MarcoLosurdo/DigiSporc/DigiSporc-board.png

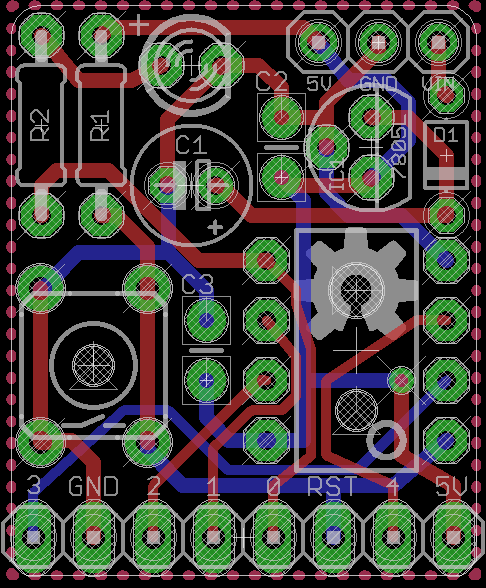
DigiSporc-board.png
