MarcoLosurdo/DigiSporc/DigiSporc.png

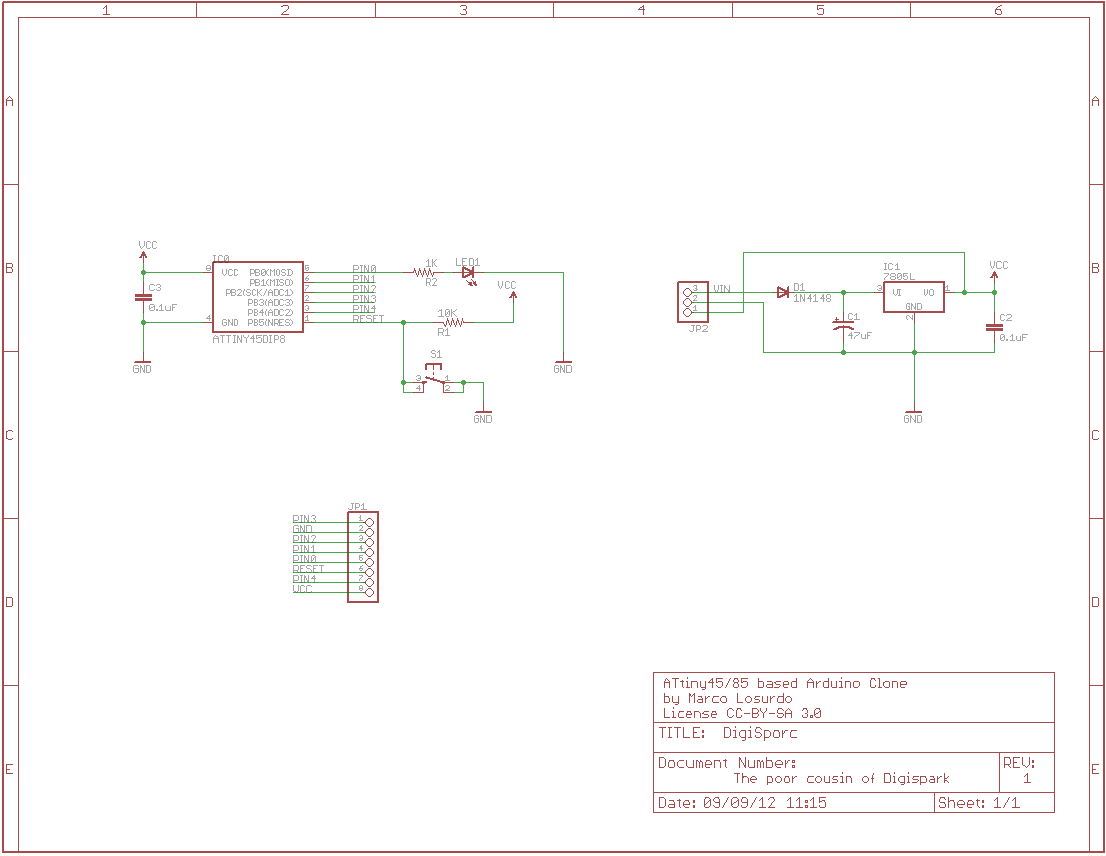
DigiSporc.png
