MarcoLosurdo/DigiSporc/DigiSporc_nano.png

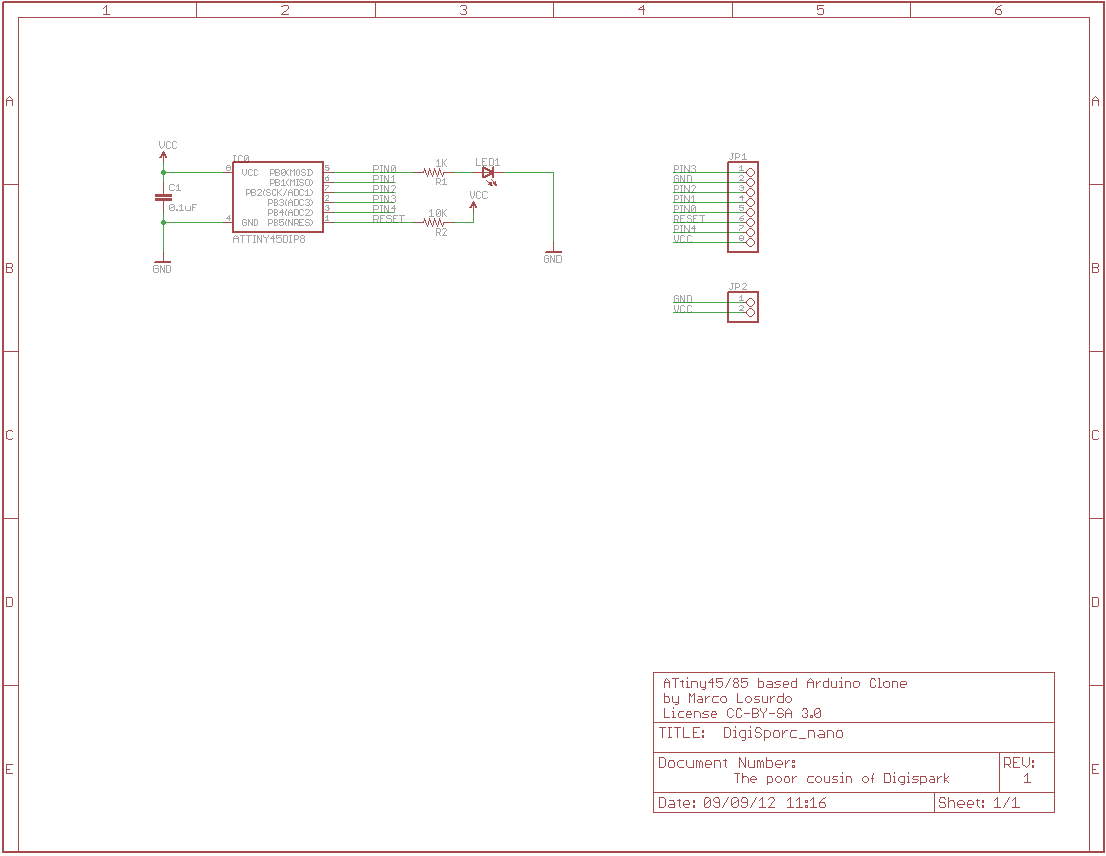
DigiSporc_nano.png
