MarcoLosurdo/DigiSporc/pic/ArduinoAsISP_menu.png

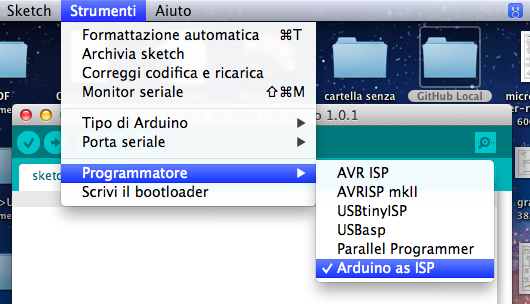
pic/ArduinoAsISP_menu.png
