MarcoLosurdo/DigiSporc/pic/buta.png

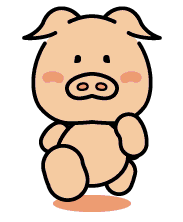
pic/buta.png
