MarcoLosurdo/DigiSporc/pic/DigiSporc proto.jpeg

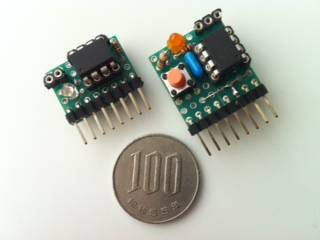
pic/DigiSporc proto.jpeg
