MarcoLosurdo/DigiSporc/pic/DigiSporc.png

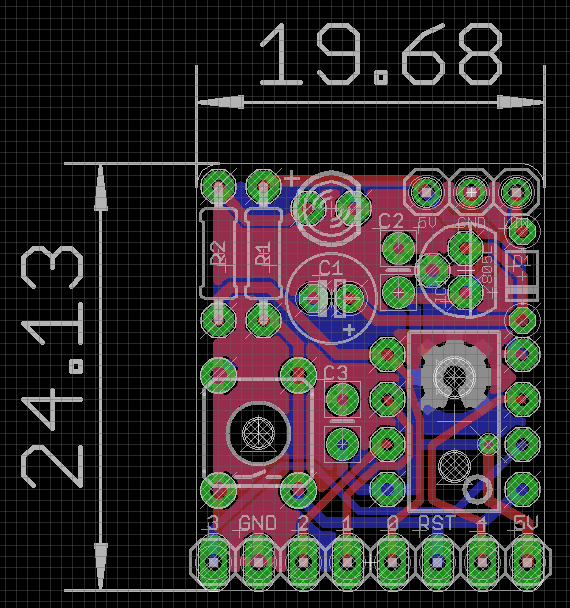
pic/DigiSporc.png
