MarcoLosurdo/DigiSporc/pic/DigiSporc_plugged.jpeg

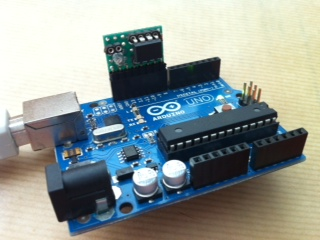
pic/DigiSporc_plugged.jpeg
