MarcoLosurdo/DigiSporc/pic/Lanciami_i_componenti.jpeg

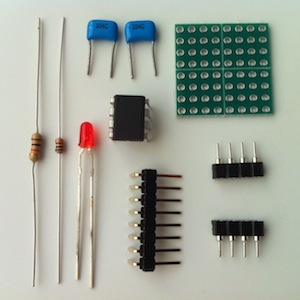
pic/Lanciami_i_componenti.jpeg
