MarcoLosurdo/DigiSporc/pic/proto.jpeg

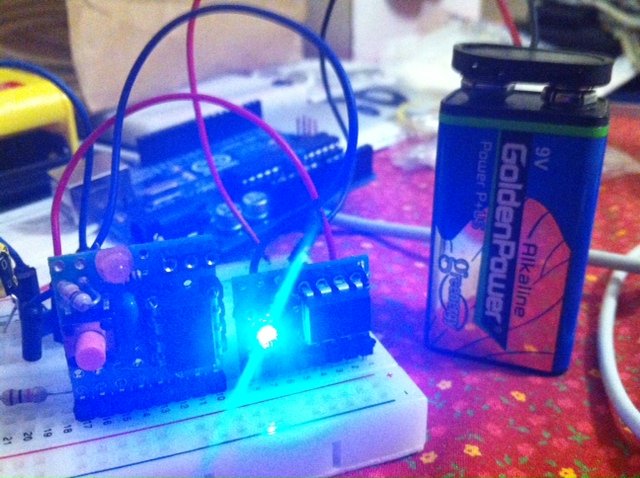
pic/proto.jpeg
