MarcoLosurdo/DigiSporc/pic/scrivi_bootloader_menu.png

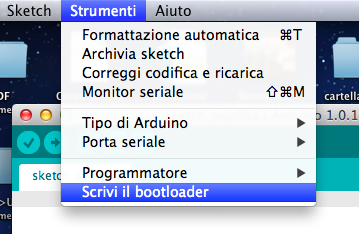
pic/scrivi_bootloader_menu.png
