MarcoLosurdo/DigiSporc/pic/size.png

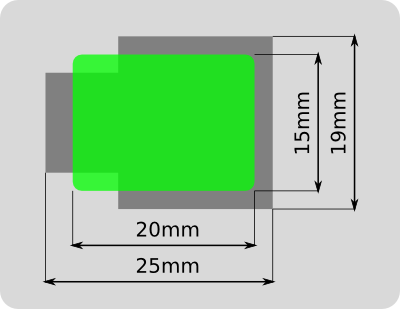
pic/size.png
